swanmatch/MxLEDBitPCB/MxLEDBitPCB-promicro/promicro-home.sch

## KiCad design MxLEDBitPCB-promicro/promicro-home.sch (2018-07-27)

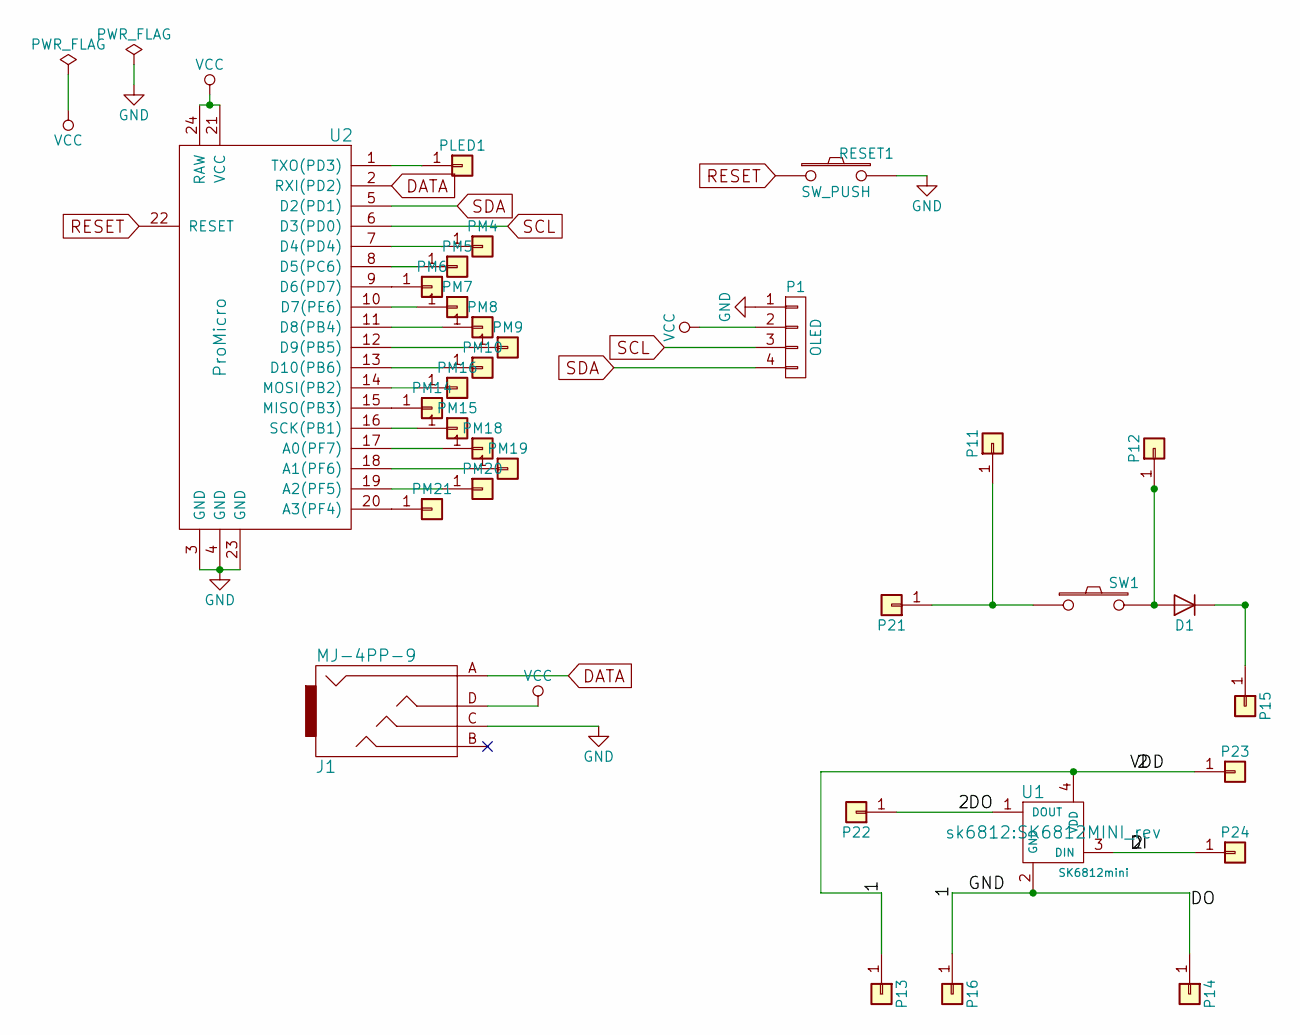
[picture p6: schematic promicro-home.sch]

Parts:
D1: D; diode
J1: MJ-4PP-9; MJ-4PP-9_rev2
P1: OLED; MY_SIL-4
P11, P12, P13, P14, P15, P16, P21, P22, P23, P24: CONN_01X01; wirepad
PLED1: CONN_01X01; wirepad
PM4, PM5, PM6, PM7, PM8, PM9, PM10, PM14, PM15, PM16, PM18, PM19, PM20, PM21: CONN_01X01; wirepad
RESET1: SW_PUSH; SW_3.5x6.0_TH
SW1: SW_PUSH; switch
U1: SK6812mini; SK6812MINI_rev
U2: ProMicro; ProMicro_rev

Connections:
1: P13.1, P14.1, P16.1, P22.1, P23.1, P24.1, U1.1 (DOUT), U1.2 (GND), U1.3 (DIN), U1.4 (VDD)
DATA: J1.A, U2.2 (RXI(PD2))
GND: J1.C, P1.1, RESET1.2, U2.3 (GND), U2.4 (GND), U2.23 (GND)
unnamed: D1.1 (K), P15.1
unnamed: D1.2 (A), P12.1, SW1.2
unnamed: P11.1, P21.1, SW1.1
unnamed: PLED1.1, U2.1 (TXO(PD3))
unnamed: PM4.1, U2.7 (D4(PD4))
unnamed: PM5.1, U2.8 (D5(PC6))
unnamed: PM6.1, U2.9 (D6(PD7))
unnamed: PM7.1, U2.10 (D7(PE6))
unnamed: PM8.1, U2.11 (D8(PB4))
unnamed: PM9.1, U2.12 (D9(PB5))
unnamed: PM10.1, U2.13 (D10(PB6))
unnamed: PM14.1, U2.15 (MISO(PB3))
unnamed: PM15.1, U2.16 (SCK(PB1))
unnamed: PM16.1, U2.14 (MOSI(PB2))
unnamed: PM18.1, U2.17 (A0(PF7))
unnamed: PM19.1, U2.18 (A1(PF6))
unnamed: PM20.1, U2.19 (A2(PF5))
unnamed: PM21.1, U2.20 (A3(PF4))
RESET: RESET1.1, U2.22 (RESET)
SCL: P1.3, U2.6 (D3(PD0))
SDA: P1.4, U2.5 (D2(PD1))
VCC: J1.D, P1.2, U2.21 (VCC), U2.24 (RAW)
