swanmatch/MxLEDBitPCB/choc/choc.sch

## KiCad design choc/choc.sch (2019-02-09)

Schematic: choc.sch

Parts:
D1, D2, D3, D4, D5, D6, D7, D8, D9, D10, D11, D12, D13, D14, D15, D16, D17, D18, D19, D20, D21, D22, D23, D24, D25: D; Diode-Hybrid-Back
L1, L2, L3, L4, L5, L6, L7, L8, L9, L10, L11, L12, L13, L14, L15, L16, L17, L18, L19, L20, L21, L22, L23, L24, L25: SK6812MINI; SK6812MINI_rev
SW1, SW2, SW3, SW4, SW5, SW6, SW7, SW8, SW9, SW10, SW11, SW12, SW13, SW14, SW15, SW16, SW17, SW18, SW19, SW20, SW21, SW22, SW23, SW24, SW25: SW_PUSH; MX_PCB_100H
